NCSU-Scout-IoT/SeniorDesignF2019/Software Files/Software Examples/Ex5_OutOfBox/adc/adc.h

/*
 * adc.h
 *
 *  Created on: Apr 21, 2019
 *      Author: Caleb
 */
#include "driverlib.h"
#include <stdio.h>

#ifndef ADC_H_
#define ADC_H_

#ifdef ADC_A4
#define ADC
#endif

void init_ADC12B(void);
void init_ADC12B_memoryBuffer(uint8_t memoryBufferControlIndex,
		uint8_t inputSourceSelect, uint16_t EOS, uint16_t IFG_mask, uint16_t IE_mask);
void ADC_initPorts(void);
void ADC_getPercentage(uint8_t buffer[], uint16_t value, uint16_t maximum);

#endif /* ADC_H_ */
