NCSU-Scout-IoT/SeniorDesignF2019/Software Files/Software Examples/Ex4_I2C/sht35.h

/*
 * sht35.h
 *
 *  Created on: Apr 8, 2019
 *      Author: caleb
 */

#include "driverlib.h"
#include <inttypes.h>
#include <stdio.h>

#ifndef SHT35_H_
#define SHT35_H_

#define RXCOUNT 6


// SHT35 Commands
#define HALF_MPS        0x20
#define ONE_MPS         0x21
#define TWO_MPS         0x22
#define FOUR_MPS        0x23
#define TEN_MPS         0x27
//
#define HALF_LOW_RP     0x2F
#define HALF_MED_RP     0x24
#define HALF_HIGH_RP    0x32
//
#define ONE_LOW_RP      0x2D
#define ONE_MED_RP      0x26
#define ONE_HIGH_RP     0x30
//
#define TWO_LOW_RP      0x2B
#define TWO_MED_RP      0x20
#define TWO_HIGH_RP     0x36
//
#define FOUR_LOW_RP     0x29
#define FOUR_MED_RP     0x22
#define FOUR_HIGH_RP    0x34
//
#define TEN_LOW_RP      0x2A
#define TEN_MED_RP      0x21
#define TEN_HIGH_RP     0x37
//

void SHT35_sendCommand(uint8_t MSB, uint8_t LSB);
void SHT35_getTemp(uint8_t data[], uint8_t buffer[]);
void SHT35_getHumidity(uint8_t data[], uint8_t buffer[]);

#endif /* SHT35_H_ */
