NCSU-Scout-IoT/SeniorDesignF2019/Software Files/Software Examples/Ex5_OutOfBox/timers.h

/*
 * timers.h
 *
 *  Created on: Apr 20, 2019
 *      Author: Caleb
 */
#include "driverlib.h"

#ifndef TIMERS_H_
#define TIMERS_H_
#define COMPARE_VALUE (30000)

void timer_a_init(uint16_t timer_a_base);


#endif /* TIMERS_H_ */
